mathigatti/tickle-machine/ref tecnicas/Ramps_interfaces.jpg

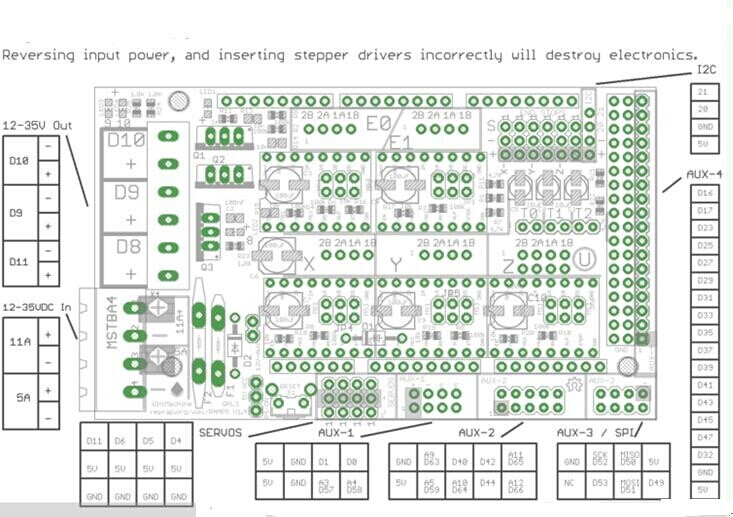
ref tecnicas/Ramps_interfaces.jpg
