mathigatti/tickle-machine/src/move/mask.png

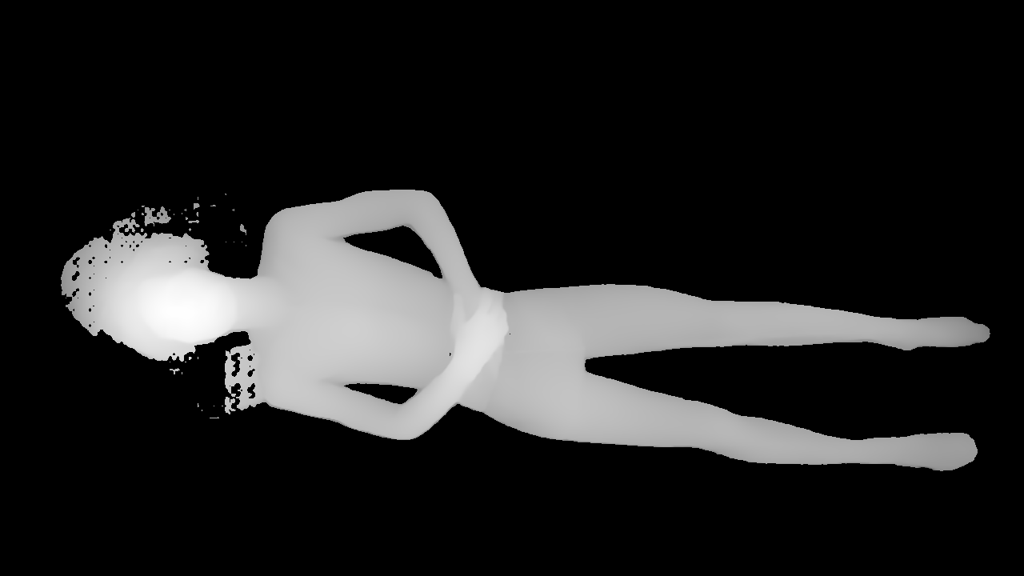
src/move/mask.png
